saketharjun12-boop/High-Performance-DAC-system/Calculations/Handwritten_Calculations/README.md

# Handwritten Calculations

Upload scans/photos/PDFs of handwritten work here.

Suggested names:
- `power_budget_notes.pdf`
- `boost_converter_notes.pdf`
- `lt3045_notes.pdf`
- `trace_width_notes.pdf`
- `analog_output_notes.pdf`
